tedelm/MultiFiller/img/mfiller_mockUp_counterpressure_01.JPG

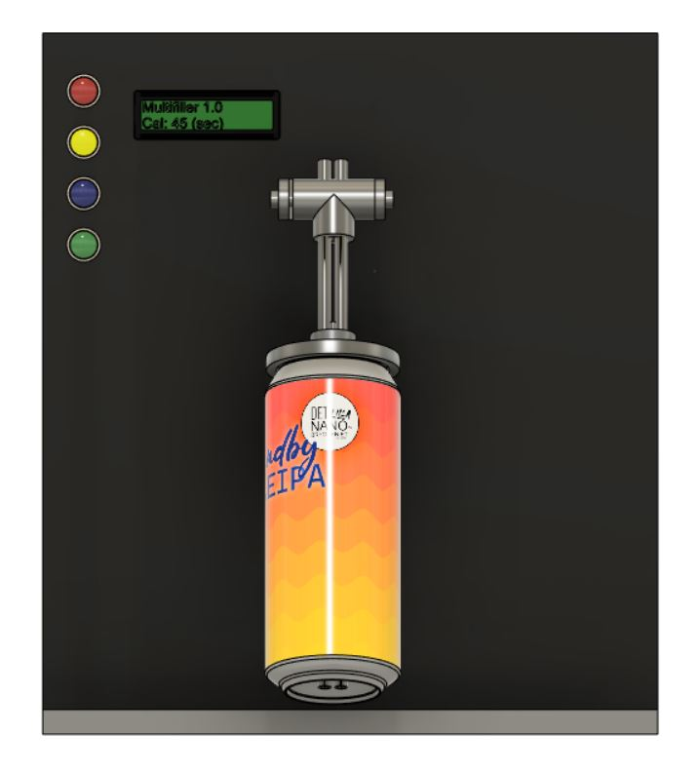
img/mfiller_mockUp_counterpressure_01.JPG
