tedelm/MultiFiller/img/mfiller_mockUp_counterpressure_02.JPG

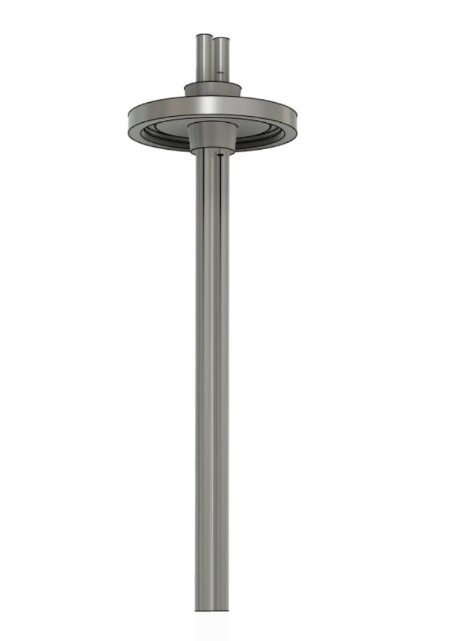
img/mfiller_mockUp_counterpressure_02.JPG
