tedelm/MultiFiller/img/mfiller_mockUp_counterpressure_03.JPG

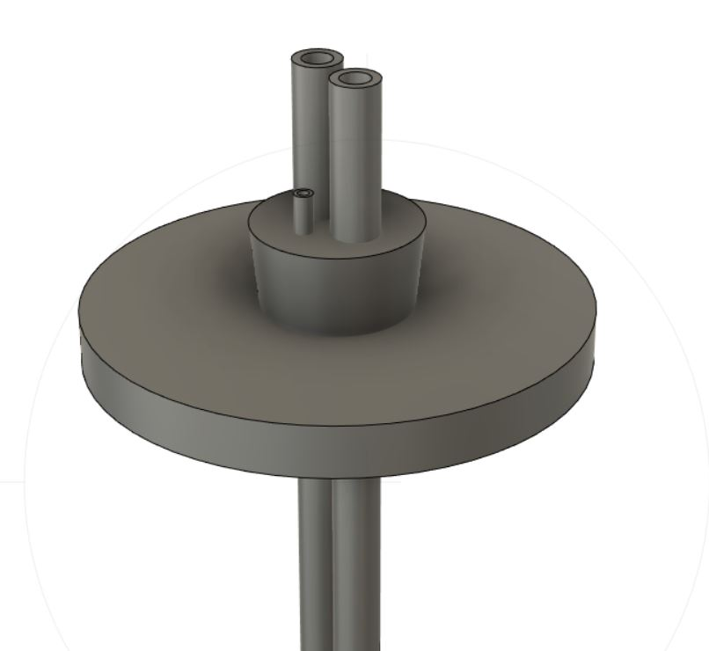
img/mfiller_mockUp_counterpressure_03.JPG
