tedelm/MultiFiller/img/mfiller_mockUp_counterpressure_05.JPG

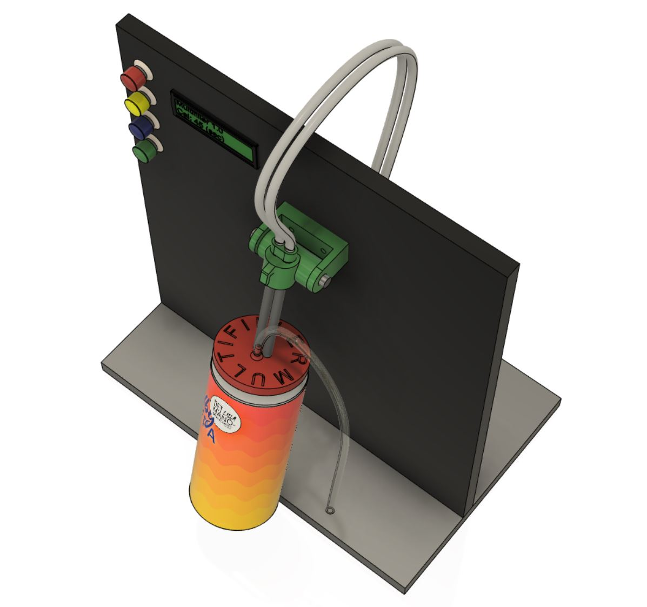
img/mfiller_mockUp_counterpressure_05.JPG
