tedelm/MultiFiller/img/mockup_33.png

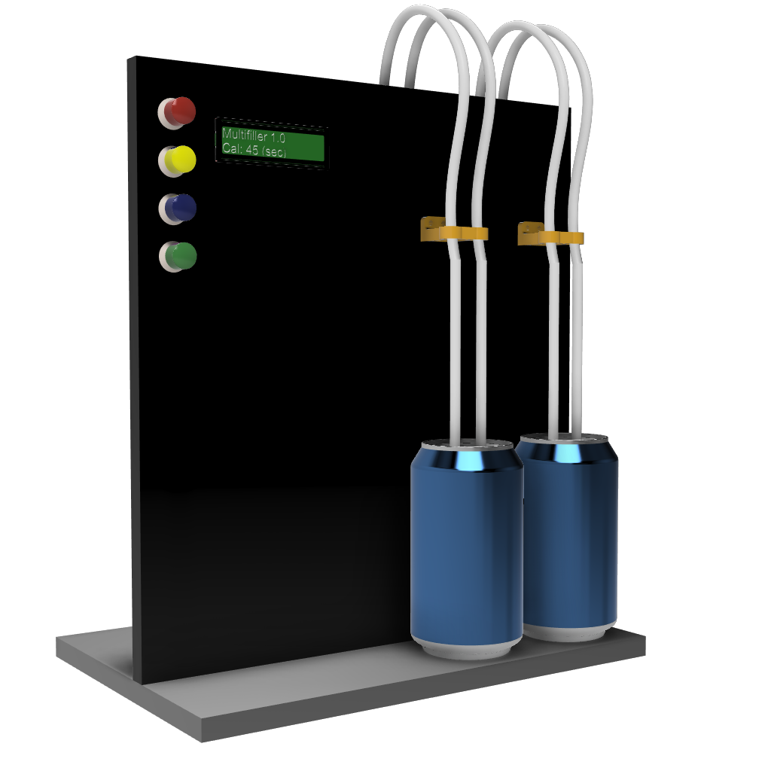
img/mockup_33.png
