tedelm/MultiFiller/img/mockup_v1.2.png

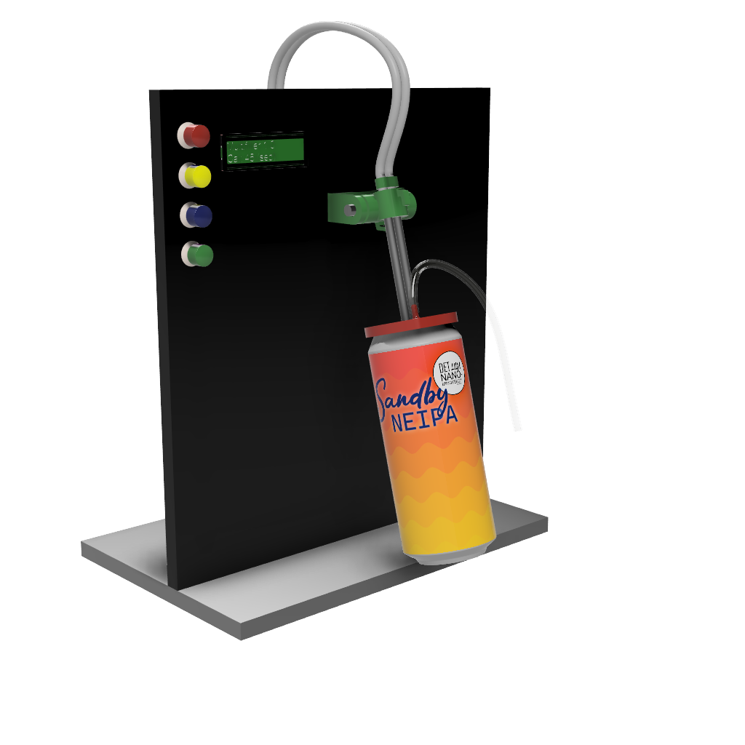
img/mockup_v1.2.png
