tedelm/MultiFiller/img/NEIPA.png

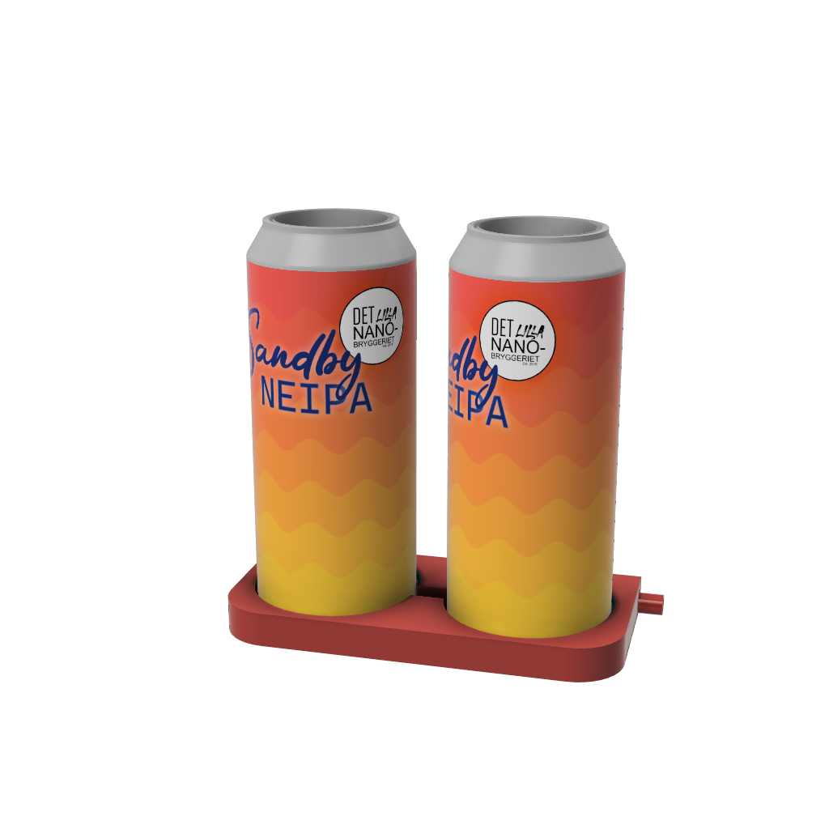
img/NEIPA.png
